maciejmiklas/dds-function-generator/LCD.h

#ifndef LCD_H_
#define LCD_H_

#include "Arduino.h"
#include "LiquidCrystal.h"
#include "Wave.h"
#include "Util.h"

void lcd_setup();
void lcd_printFreqStep(uint16_t reqStep);
void lcd_printFreq(Frequency* freq);
void lcd_printWave(WaveDef wave);

#endif /* LCD_H_ */
